Abdelrahman-Elnahrawy/EEV20.1/Render Prev images/2 Idle Valves.PNG

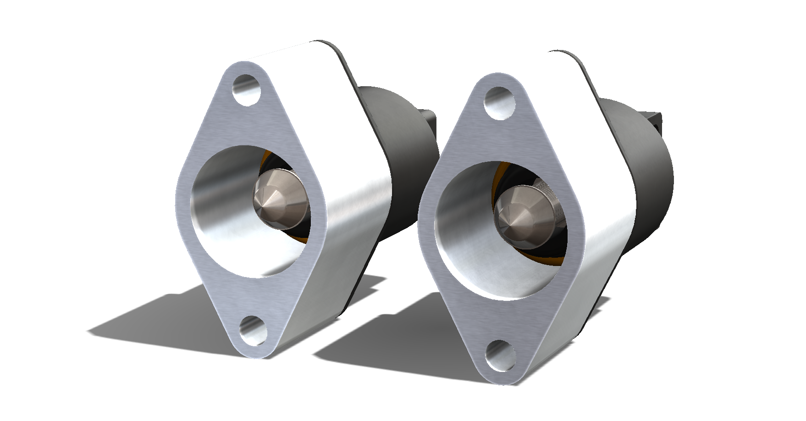
Render Prev images/2 Idle Valves.PNG
